AlyonaSl/test/output/preview_axle.png

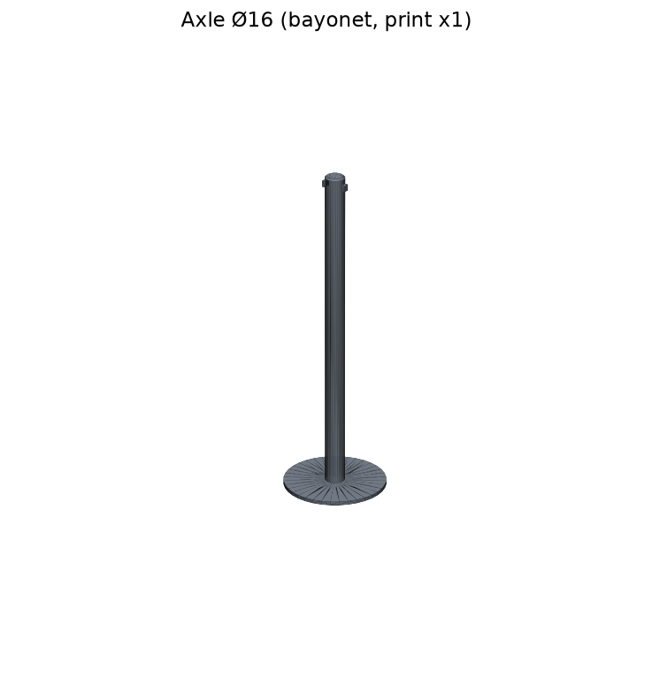
output/preview_axle.png
