AlyonaSl/test/output/preview_clamp_screw.png

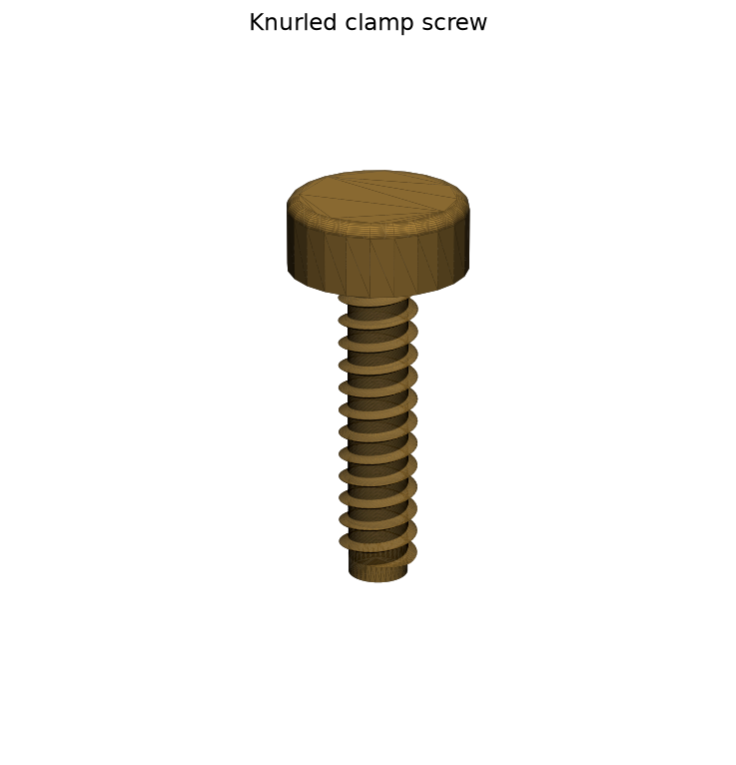
output/preview_clamp_screw.png
