AlyonaSl/test/output/preview_fixator.png

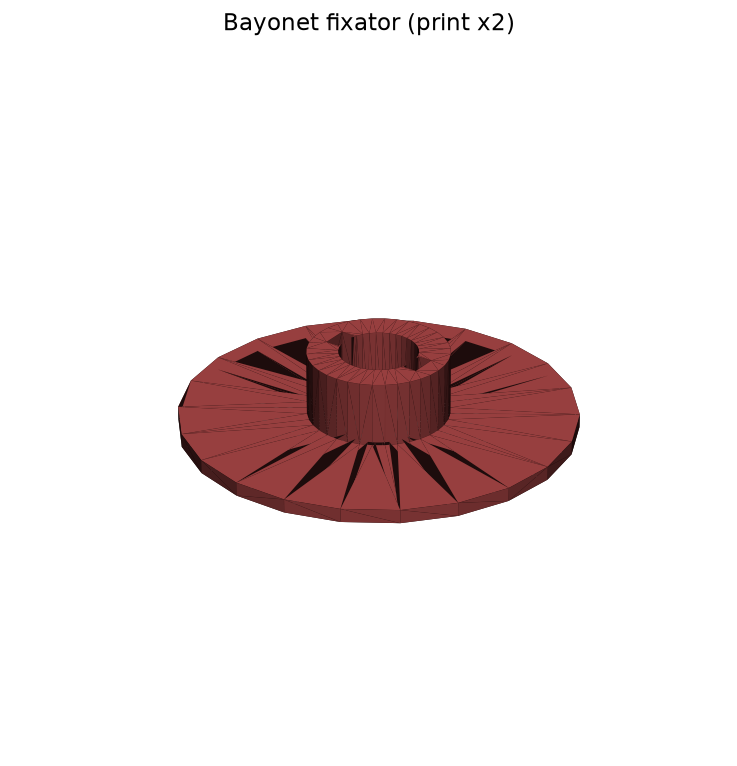
output/preview_fixator.png
