AlyonaSl/test/output/scad/preview_accessories.png

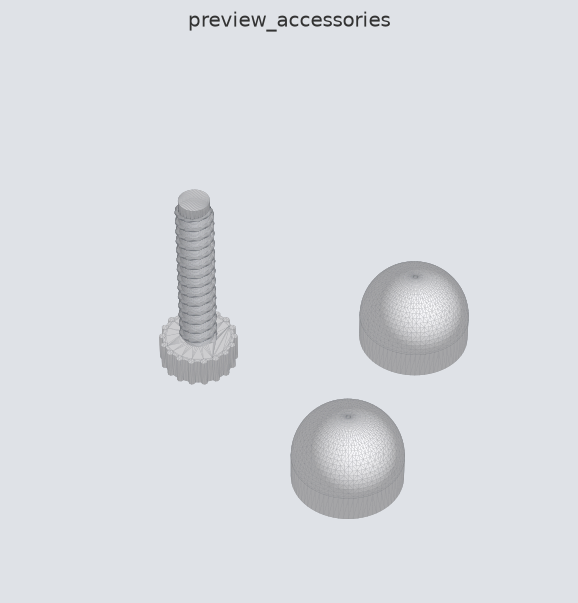
output/scad/preview_accessories.png
