AlyonaSl/test/output/scad/preview_axle.png

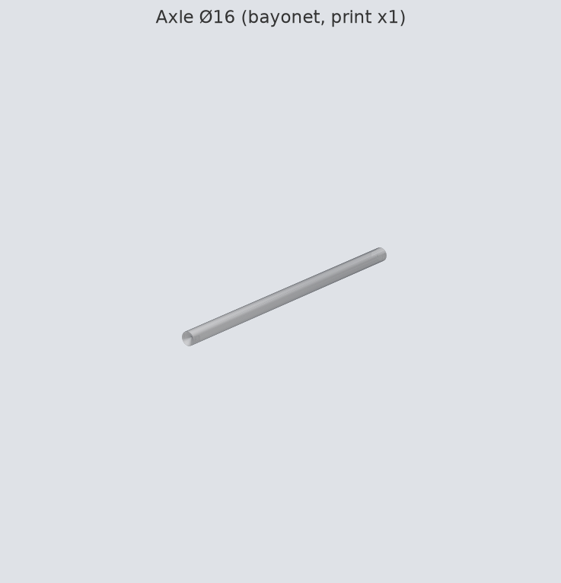
output/scad/preview_axle.png
