AlyonaSl/test/output/scad/preview_lock.png

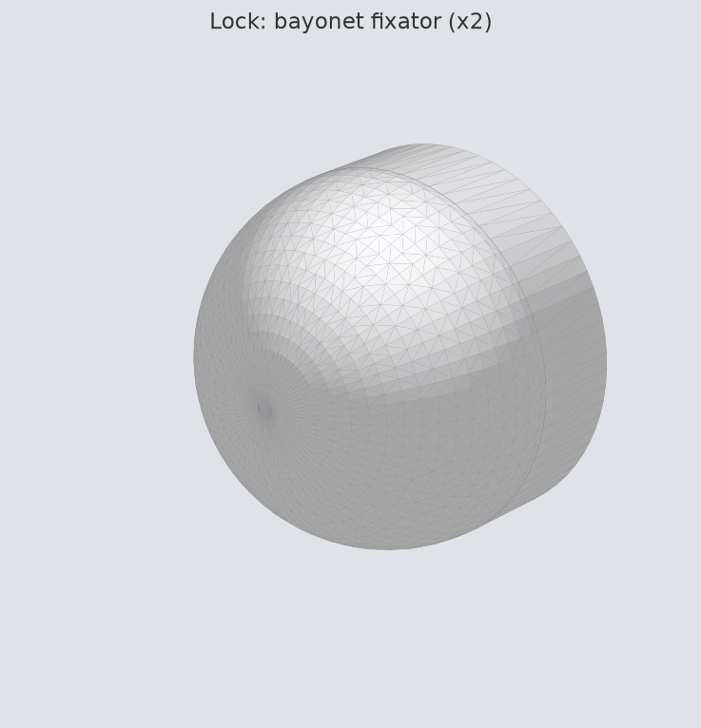
output/scad/preview_lock.png
