AlyonaSl/test/output/preview_assembly.png

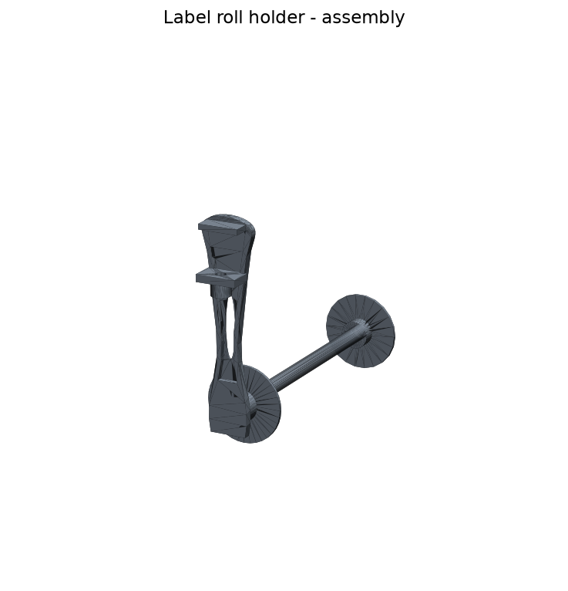
output/preview_assembly.png
